etashj/banana-split/models/mal12pin.step

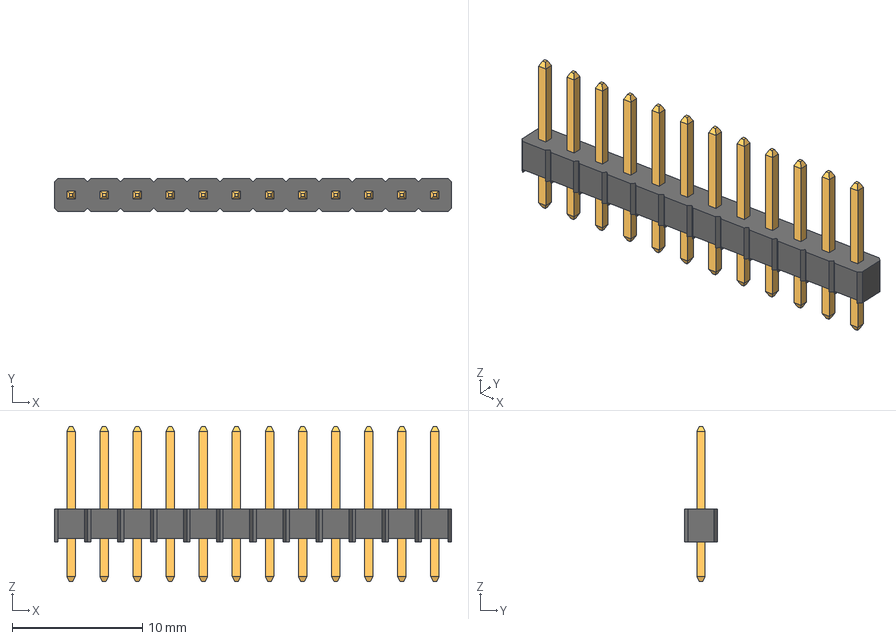
[picture p23: CAD file, 2025-07-06]
models/mal12pin.step
30.5 x 2.54 x 11.9 mm
