etashj/banana-split/models/jstph.stp

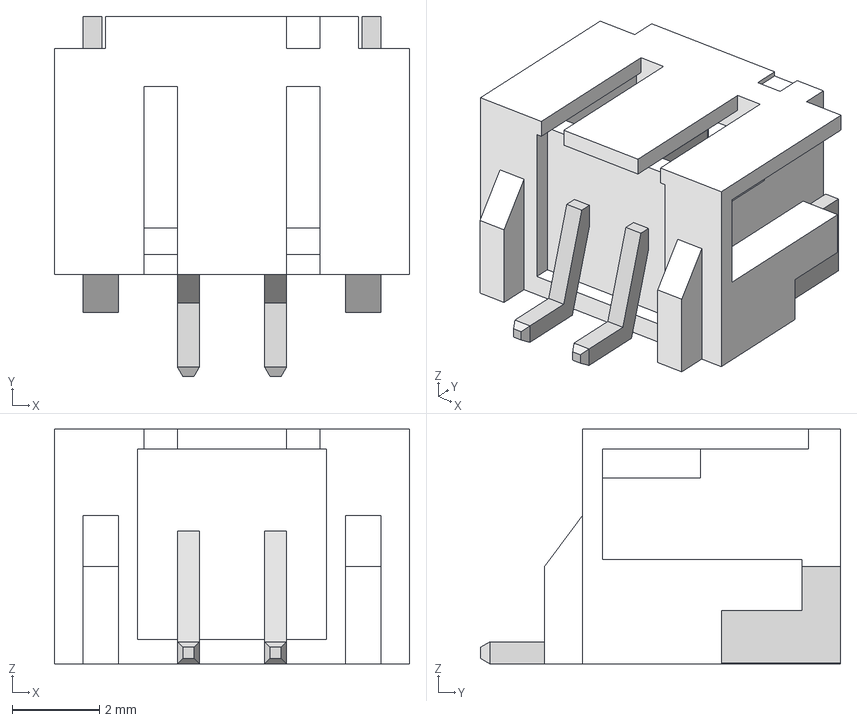
[picture p24: CAD file, 2025-07-06]
models/jstph.stp
8.15 x 8.26 x 5.38 mm
