etashj/banana-split/models/mal5pin.step

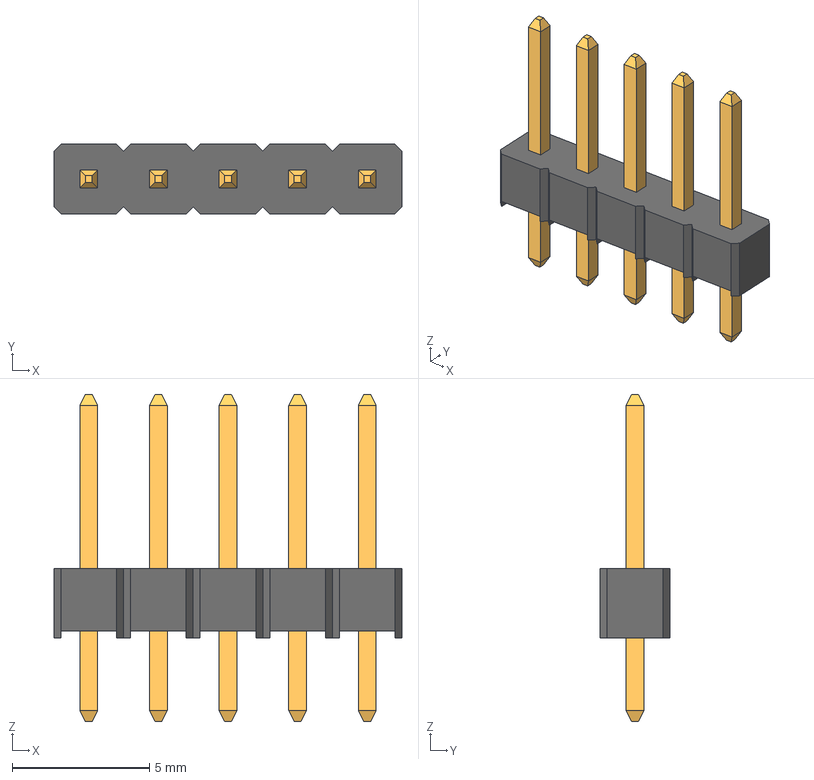
[picture p25: CAD file, 2025-07-06]
models/mal5pin.step
12.7 x 2.54 x 11.9 mm
