etashj/banana-split/models/fem12pin.step

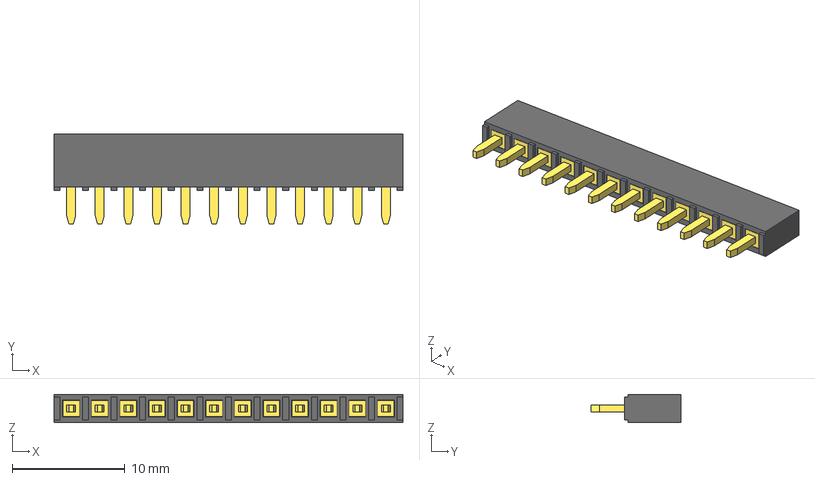
[picture p26: CAD file, 2025-07-06]
models/fem12pin.step
31.0 x 8.00 x 2.50 mm
